pk17r/Ultimate_Tester/ComponentTester-1.54m/Arduino Mega Pinout.png

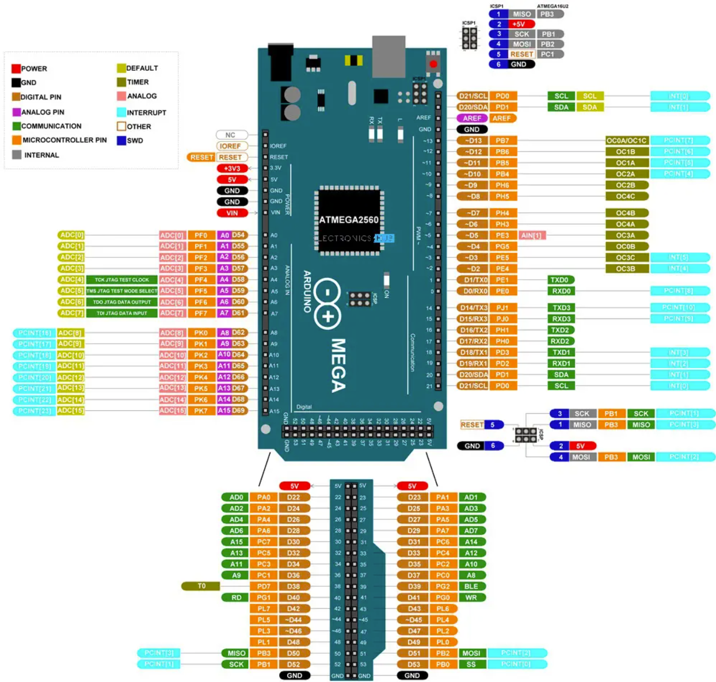
ComponentTester-1.54m/Arduino Mega Pinout.png
