pk17r/Ultimate_Tester/ComponentTester-1.54m/atmega1284p_pinout.png

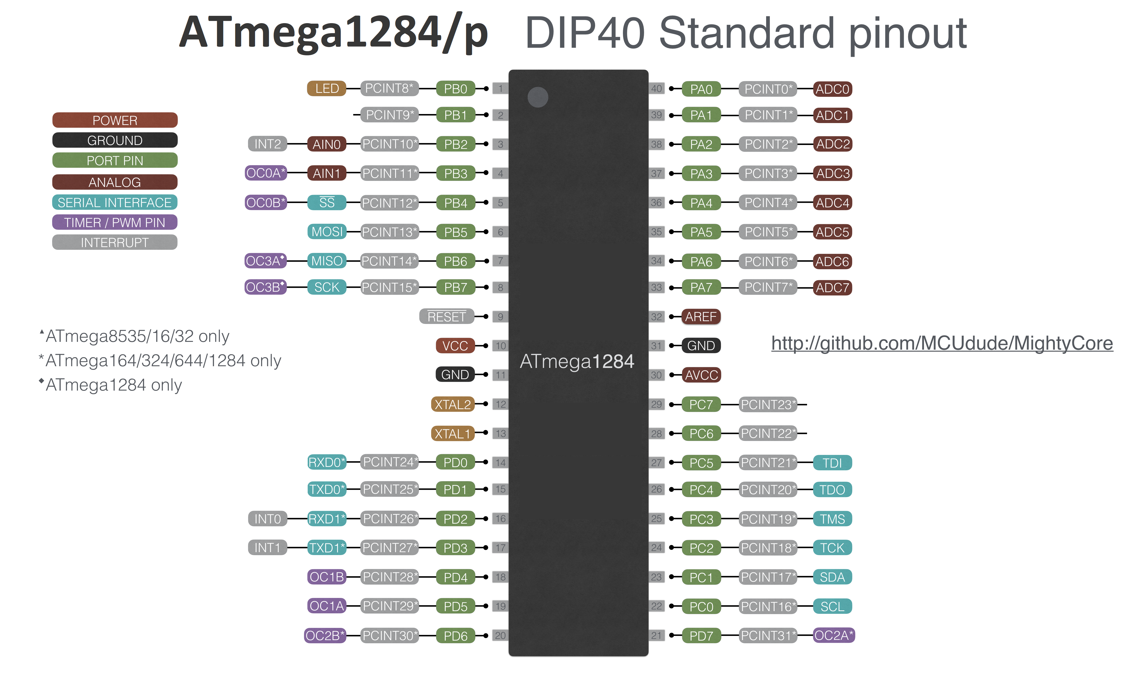
ComponentTester-1.54m/atmega1284p_pinout.png
