pk17r/Ultimate_Tester/Ultimate_Tester_PCBs/UltimateTester_v1_with_mods/Schematics.png

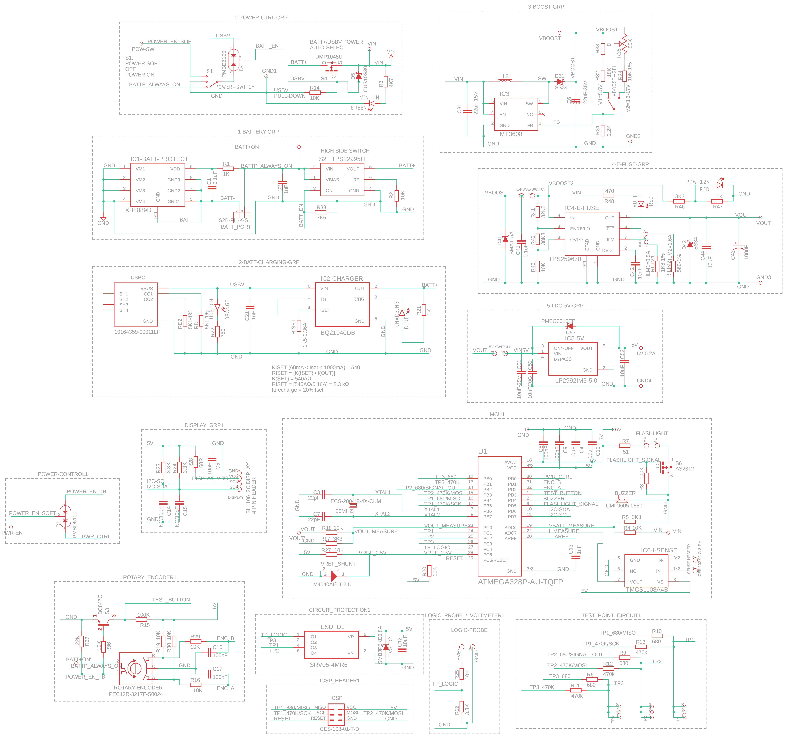
Ultimate_Tester_PCBs/UltimateTester_v1_with_mods/Schematics.png
