pk17r/Ultimate_Tester/ComponentTester-1.54m/AVR_Dudess_Settings.jpg

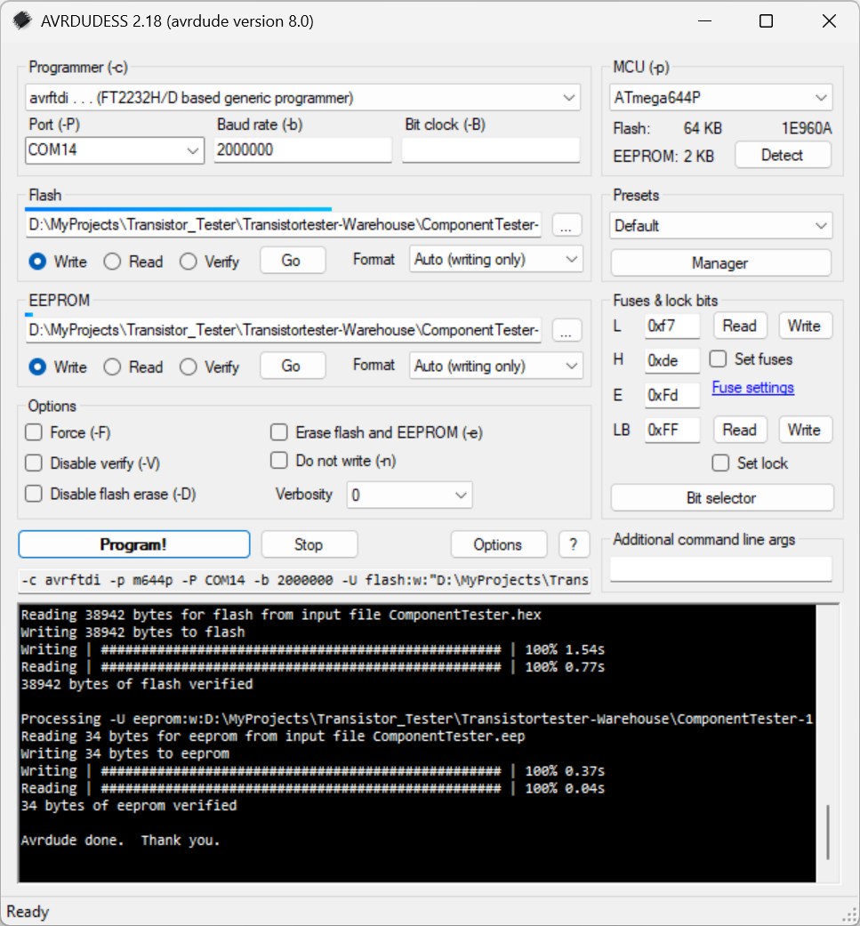
ComponentTester-1.54m/AVR_Dudess_Settings.jpg
