pk17r/Ultimate_Tester/Ultimate_Tester_PCBs/UltimateTester_v1_Pics/20250103_011226.jpg

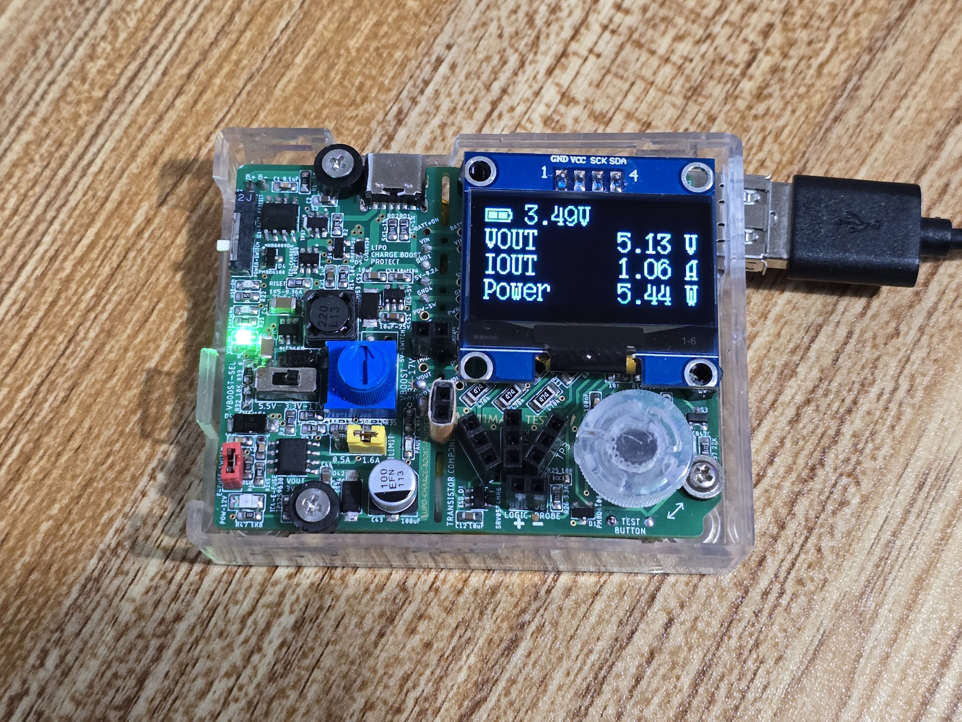
Ultimate_Tester_PCBs/UltimateTester_v1_Pics/20250103_011226.jpg
