pk17r/Ultimate_Tester/Ultimate_Tester_PCBs/UltimateTester_v1_Pics/img_0640.png

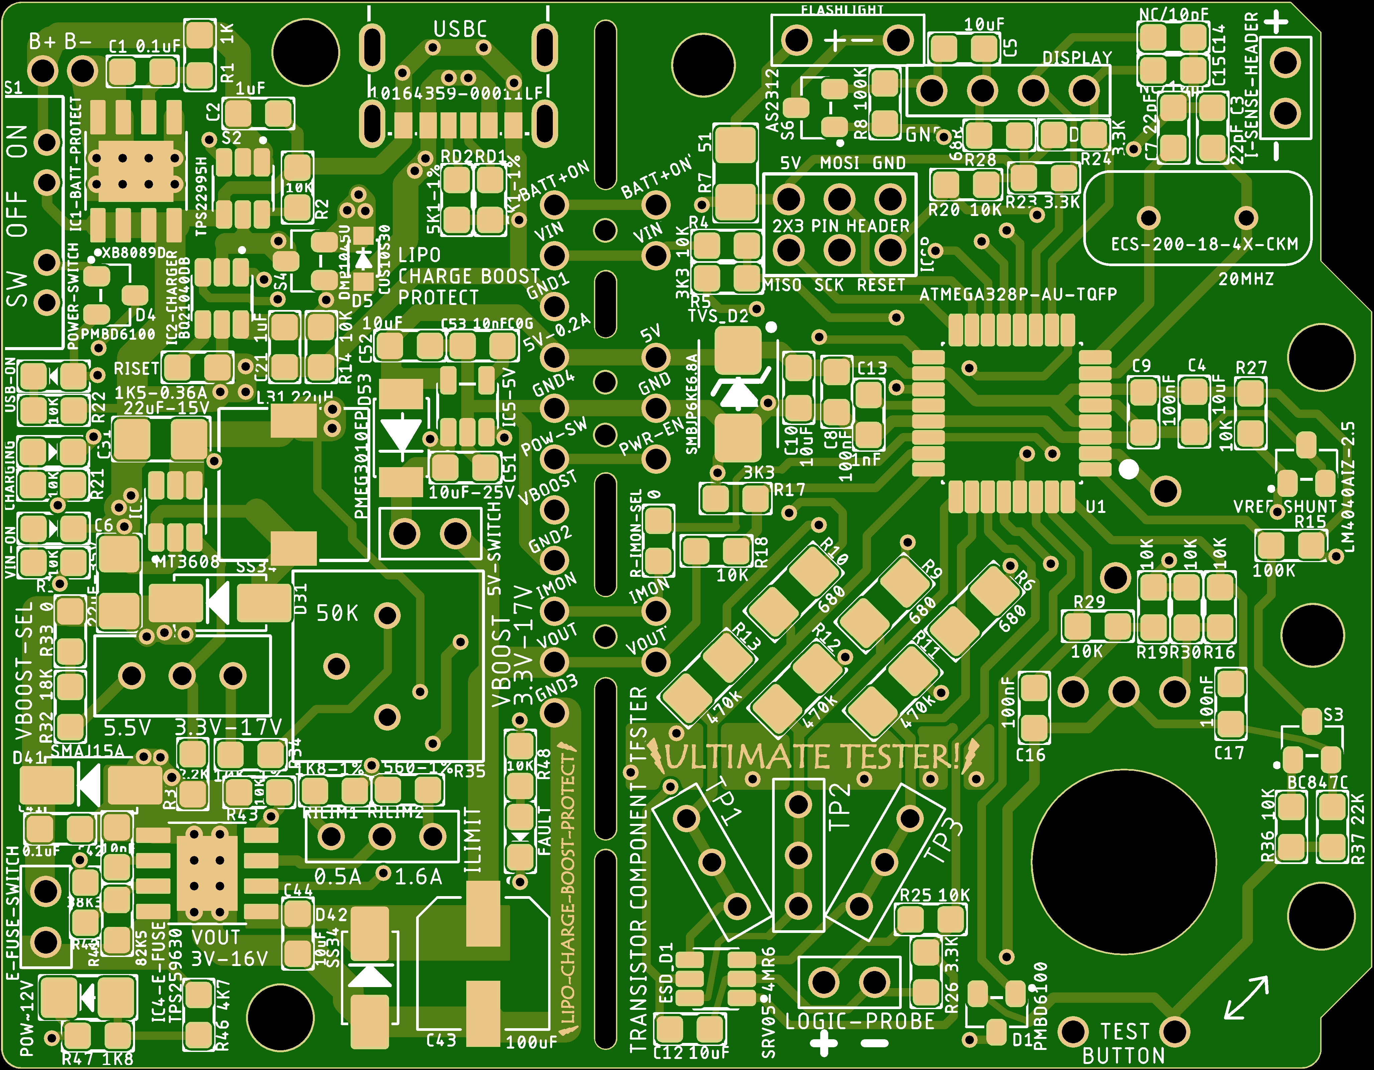
Ultimate_Tester_PCBs/UltimateTester_v1_Pics/img_0640.png
