pk17r/Ultimate_Tester/Ultimate_Tester_PCBs/UltimateTester_v1_Pics/img_0926.jpg

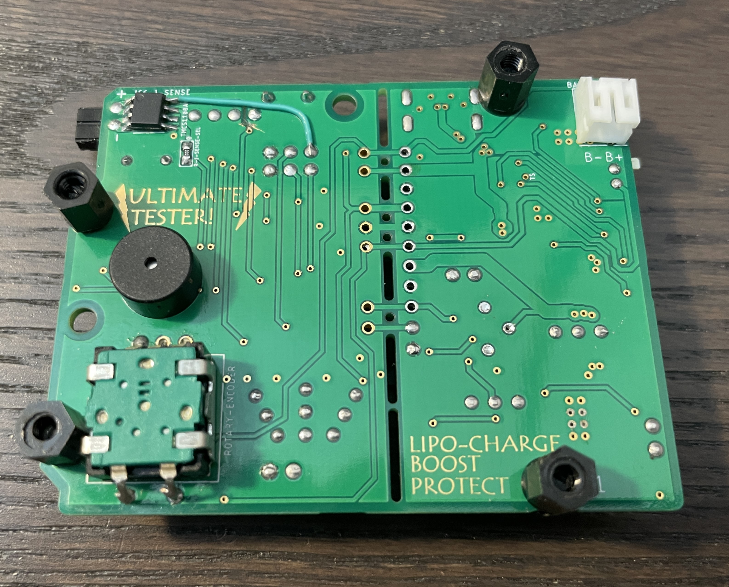
Ultimate_Tester_PCBs/UltimateTester_v1_Pics/img_0926.jpg
