pk17r/Ultimate_Tester/Ultimate_Tester_PCBs/UltimateTester_v1_Pics/main_image.jpg

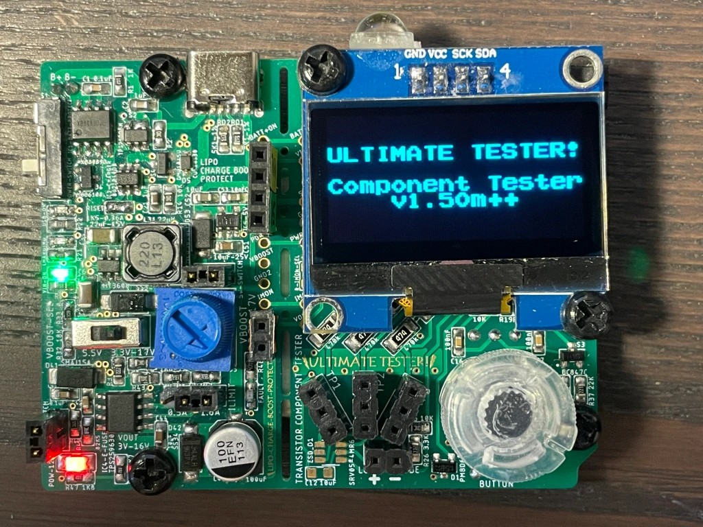
Ultimate_Tester_PCBs/UltimateTester_v1_Pics/main_image.jpg
