pk17r/Ultimate_Tester/Ultimate_Tester_PCBs/UltimateTester_v2.1/3D_UltimateTester_v2.1_2025-12-15_Btm.png

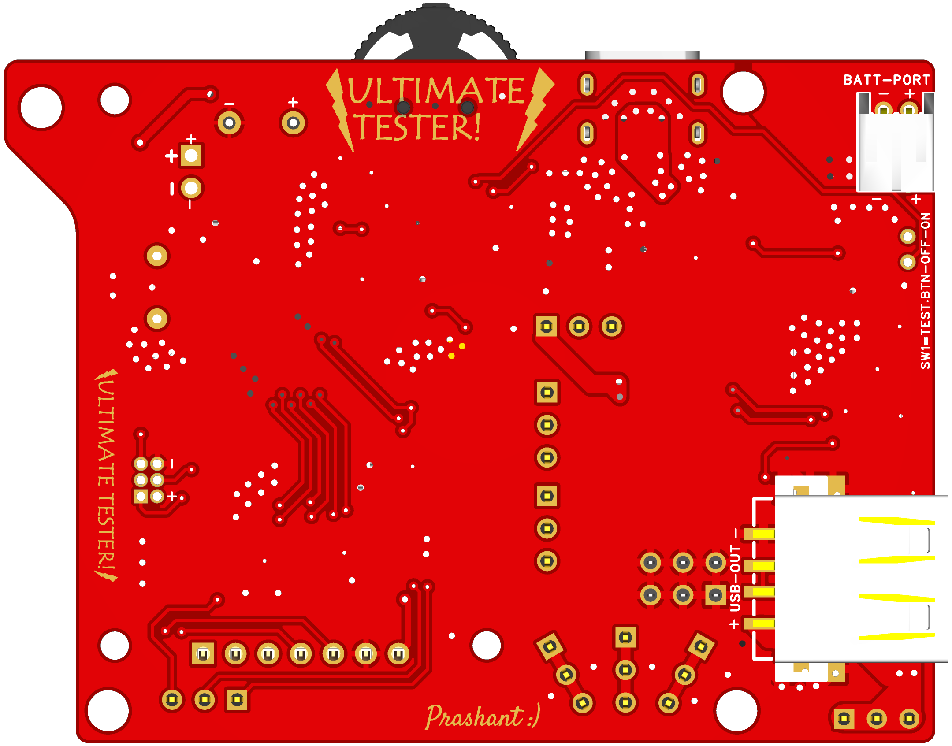
Ultimate_Tester_PCBs/UltimateTester_v2.1/3D_UltimateTester_v2.1_2025-12-15_Btm.png
