pk17r/Ultimate_Tester/Firmware/k-firmware/trunk/ReadInductance.c

// new code by K.-H. Kübbeler
// The 680 Ohm resistor (R_L_VAL) at the Lowpin will be used as current sensor
// The current with a coil will with (1 - e**(-t*R/L)), where R is
// the sum of Pin_RM , R_L_VAL , Resistance of coil and Pin_RP.
// L in the inductance of the coil.
#include <avr/io.h>
#include <stdlib.h>
#include "Transistortester.h"


//=================================================================
void ReadInductance(void) {
#if FLASHEND > 0x1fff
  // check if inductor and measure the inductance value
  unsigned int tmpint;
  unsigned int umax;
  unsigned int total_r;		// total resistance of current loop
  unsigned int mess_r;		// value of resistor used for current measurement
  unsigned long inductance[4];	// four inductance values for different measurements
  union t_combi{
  unsigned long dw;     // time_constant
  uint16_t w[2];
  } timeconstant;
  unsigned int resistor;
  uint8_t res_num;
  uint16_t per_ref1,per_ref2;	// percentage
  uint8_t LoPinR_L;	// Mask for switching R_L resistor of low pin
  uint8_t HiADC;	// Mask for switching the high pin direct to VCC
  uint8_t ii;
  uint8_t count;	// counter for the different measurements
  uint8_t cnt_diff;     // resistance dependent offset
  int8_t ukorr;		// correction of comparator voltage
  uint8_t nr_pol1;	// number of successfull inductance measurement with polarity 1
  uint8_t nr_pol2;	// number of successfull inductance measurement with polarity 2
  union {
  uint16_t pw;		// return value from Rnum2pins()
  uint8_t pb[2];	// the pin numbers LowPin and HighPin
  } rpins;	// resistor pin structure to prevent two return parameters


  inductor_lpre = 2;	// H units, mark inductor as 1, if resistor is too big
  if(PartFound != PART_RESISTOR) {
     return;	//We have found no resistor  
  }
  if (ResistorsFound != 1) {
     return;	// do not search for inductance, more than 1 resistor
  }
     res_num = ResistorList[0];
     if (ResistorVal[res_num] > 21000) return;
     resistor = ResistorVal[res_num];

     // we can check for Inductance, if resistance is below 2100 Ohm
     for (count=0;count<4;count++) {
        // Try four times (different direction and with delayed counter start)
        if (count < 2) {
           // first and second pass, direction 1
           rpins.pw = Rnum2pins(res_num);	// compute the two pinnumbers for resistor res_num
        } else {
           // third and fourth pass, direction 2
           rpins.pw = Rnum2pins(res_num);	// compute the two pinnumbers for resistor res_num
           ii = rpins.pb[0];
           rpins.pb[0] = rpins.pb[1];		// swap the pins LowPin and HighPin
           rpins.pb[1] = ii;
        }
#if (((PIN_RL1 + 1) != PIN_RH1) || ((PIN_RL2 + 1) != PIN_RH2) || ((PIN_RL3 + 1) != PIN_RH3))
        HiADC = pgm_read_byte((&PinRLRHADCtab[6])+rpins.pb[1]-TP1);	// Table of ADC Pins including | TXD_VAL
#else
        HiADC = pgm_read_byte((&PinRLRHADCtab[3])+rpins.pb[1]-TP1);	// Table of ADC Pins including | TXD_VAL
#endif
        LoPinR_L = pgm_read_byte(&PinRLRHADCtab[rpins.pb[0]]-TP1);	//R_L mask for HighPin R_L load
        //==================================================================================
        // Measurement of Inductance values
        R_PORT = 0;		// switch R port to GND
        ADC_PORT =   TXD_VAL;		// switch ADC-Port to GND
        if ((resistor < 240) && ((count & 0x01) == 0)) {
           // we can use PinR_L for measurement
           mess_r = RR680MI - R_L_VAL;			// use only pin output resistance
           ADC_DDR = HiADC | (1<<rpins.pb[0]) | TXD_MSK;	// switch HiADC and Low Pin to GND, 
        } else {
           R_DDR = LoPinR_L;   		// switch R_L resistor port for LowPin to output (GND)
           ADC_DDR = HiADC | TXD_MSK;	// switch HiADC Pin to GND 
           mess_r = RR680MI;			// use 680 Ohm and PinR_L for current measurement
        }
        // Look, if we can detect any current
        for (ii=0;ii<20;ii++) {
            // wait for current is near zero
            umax = W10msReadADC(rpins.pb[0]);
            total_r =  ReadADC(rpins.pb[1]);
            if ((umax < CAP_EMPTY_LEVEL) && (total_r < CAP_EMPTY_LEVEL)) break;	// low current detected
        }
        // setup Analog Comparator
        ADC_COMP_CONTROL = (1<<ACME);			//enable Analog Comparator Multiplexer
        ACSR =  (1<<ACBG) | (1<<ACI)  | (1<<ACIC);	// enable, 1.3V, no Interrupt, Connect to Timer1 
        ADMUX = (1<<REFS0) | rpins.pb[0];			// switch Mux to Low-Pin
        ADCSRA = (1<<ADIF) | AUTO_CLOCK_DIV; //disable ADC
   
      // setup Counter1
        timeconstant.w[1] = 0;		// set ov counter to 0
        TCCR1A = 0;			// set Counter1 to normal Mode
        TCNT1 = 0;			//set Counter to 0
        TI1_INT_FLAGS = (1<<ICF1) | (1<<OCF1B) | (1<<OCF1A) | (1<<TOV1);	// reset TIFR or TIFR1
//        HiADC |= TXD_VAL;
        wait200us();			// wait for bandgap to start up
        if ((count & 0x01) == 0 ) {
           //first start counter, then start current
           TCCR1B =  (1<<ICNC1) | (0<<ICES1) | (1<<CS10);	//start counter 1MHz or 8MHz
           ADC_PORT = HiADC;		// switch ADC-Port to VCC
        } else {
           //first start current, then start counter with delay
           //parasitic capacity of coil can cause high current at the beginning
           ADC_PORT = HiADC;		// switch ADC-Port to VCC
      #if F_CPU >= 8000000UL
           wait3us();		// ignore current peak from capacity
      #else
           wdt_reset();			// delay
           wdt_reset();			// delay
      #endif
           TI1_INT_FLAGS = (1<<ICF1);	// Reset Input Capture
           TCCR1B =  (1<<ICNC1) | (0<<ICES1) | (1<<CS10);	//start counter 1MHz or 8MHz
        }
      
      //******************************
        while(1) {
           // Wait, until  Input Capture is set
           ii = TI1_INT_FLAGS;		//read Timer flags
           if (ii & (1<<ICF1))  {
              break;
           }
           if((ii & (1<<TOV1))) {		// counter overflow, 65.536 ms @ 1MHz, 8.192ms @ 8MHz
              TI1_INT_FLAGS = (1<<TOV1);	// Reset OV Flag
              wdt_reset();
              timeconstant.w[1]++;		// count one OV
              if(timeconstant.w[1] == (F_CPU/100000UL)) {
                 break; 	//Timeout for Charging, above 0.65 s
              }
           }
        }
        ADC_PORT = TXD_VAL;		// switch ADC-Port to GND
        TCCR1B = (0<<ICNC1) | (0<<ICES1) | (0<<CS10);  // stop counter
        TI1_INT_FLAGS = (1<<ICF1);			// Reset Input Capture
        timeconstant.w[0] = ICR1;		// get previous Input Capture Counter flag
      // check actual counter, if an additional overflow must be added
        if((TCNT1 > timeconstant.w[0]) && (ii & (1<<TOV1))) {
           // this OV was not counted, but was before the Input Capture
           TI1_INT_FLAGS = (1<<TOV1);		// Reset OV Flag
           timeconstant.w[1]++;			// count one additional OV
        }

//        ADC_PORT = TXD_VAL;		// switch ADC-Port to GND
        ADCSRA = (1<<ADEN) | (1<<ADIF) | AUTO_CLOCK_DIV; //enable ADC
        for (ii=0;ii<20;ii++) {
            // wait for current is near zero
            umax = W10msReadADC(rpins.pb[0]);
            total_r =  ReadADC(rpins.pb[1]);
            if ((umax < CAP_EMPTY_LEVEL) && (total_r < CAP_EMPTY_LEVEL)) break;	// low current detected
        }  /* end for ii */
  #define CNT_ZERO_42 6
  #define CNT_ZERO_720 7
//#if F_CPU == 16000000UL
//  #undef CNT_ZERO_42
//  #undef CNT_ZERO_720
//  #define CNT_ZERO_42 7
//  #define CNT_ZERO_720 10
//#endif
        total_r = (mess_r + resistor + RRpinMI);
//        cnt_diff = 0;
//        if (total_r > 7000) cnt_diff = 1;
//        if (total_r > 14000) cnt_diff = 2;
        cnt_diff = total_r / ((14000UL * 8) / (F_CPU/1000000UL));
        tmpint = ref_mv_offs;		// corrected reference voltage (for C)
        if (mess_r < R_L_VAL) {
           // measurement without 680 Ohm
           cnt_diff = CNT_ZERO_42;
           if (timeconstant.dw < 225) {
              ukorr = (timeconstant.w[0] / 5) - 20;
           } else {
              ukorr = 25;
           }
           tmpint -= (((REF_L_KORR * 10) / 10) + ukorr);
        } else {
           // measurement with 680 Ohm resistor
           // if 680 Ohm resistor is used, use REF_L_KORR for correction
           cnt_diff += CNT_ZERO_720;
           tmpint += REF_L_KORR;
        }
        if (timeconstant.dw > cnt_diff) timeconstant.dw -= cnt_diff;
        else          timeconstant.dw = 0;
       
        if ((count&0x01) == 1) {
           // second pass with delayed counter start
           timeconstant.dw += (3 * (F_CPU/1000000UL))+10;
        }
        if (timeconstant.w[1] >= (F_CPU/100000UL)) timeconstant.dw = 0; // no transition found
        if (timeconstant.dw > 10) {
           timeconstant.dw -= 1;
        }
        // compute the maximum Voltage umax with the Resistor of the coil
        umax = ((unsigned long)mess_r * (unsigned long)ADCconfig.U_AVCC) / total_r;
        per_ref1 = ((unsigned long)tmpint * 1000) / umax;
//        per_ref2 = (uint8_t)MEM2_read_byte(&LogTab[per_ref1]);	// -log(1 - per_ref1/100)
        per_ref2 = get_log(per_ref1);		// -1000*log(1 - per_ref1/1000)
/* ********************************************************* */
#if 0
          if (count == 0) {
             lcd_line3();
             DisplayValue(count,0,' ',4);
             DisplayValue(timeconstant.dw,0,'+',4);
             DisplayValue(cnt_diff,0,' ',4);
             DisplayValue(total_r,-1,'r',4);
             lcd_space();
             DisplayValue(per_ref1,-1,'%',4);
             lcd_line4();
             Display_mV(tmpint,4);
             lcd_space();
             Display_mV(umax,4);
             lcd_space();
             DisplayValue(per_ref2,-1,'%',4);
             wait_about4s();	// debug delay
             wait_about2s();	// debug delay
          }
#endif
/* ********************************************************* */
        // inductor_lx in 0.01mH units,  L = Tau * R
        per_ref1 = ((per_ref2 * (F_CPU/1000000UL)) + 5) / 10;
        inductance[count] = (timeconstant.dw * total_r ) / per_ref1;
        if (((count&0x01) == 0) && (timeconstant.dw > ((F_CPU/1000000UL)+3))) {
           // transition is found, measurement with delayed counter start is not necessary
           inductance[count+1] = inductance[count];	// set delayed measurement to same value
           count++;		// skip the delayed measurement
        }
        wdt_reset();
     }  //end for count
     ADC_PORT = TXD_VAL;		// switch ADC Port to GND
     wait_about20ms();
     nr_pol1 = 0;
     if (inductance[1] > inductance[0]) { nr_pol1 = 1; } 
     nr_pol2 = 2;
     if (inductance[3] > inductance[2]) { nr_pol2 = 3; } 
     if (inductance[nr_pol2] < inductance[nr_pol1]) nr_pol1 = nr_pol2;
     inductor_lx = inductance[nr_pol1];
     inductor_lpre = -5;	// 10 uH units
     if (((nr_pol1 & 1) == 1) || (resistor >= 240)) {
        // with 680 Ohm resistor total_r is more than 7460
        inductor_lpre = -4;	// 100 uH units
        inductor_lx = (inductor_lx + 5) / 10;
     } 
     if (inductor_lx == 0) inductor_lpre = 0;	//mark as zero

  // switch all ports to input
  ADC_DDR =  TXD_MSK;		// switch all ADC ports to input
  R_DDR = 0;			// switch all resistor ports to input
#endif
  return;
 } // end ReadInductance()
