pk17r/Ultimate_Tester/TT+ADS1115/ads1115.c

#include <util/delay.h>
#include "ads1115.h"

//*************************************************************************
//  write register of ADC
uint8_t ads1115_write_register(uint8_t addr, uint8_t reg, uint16_t data){	
	i2c_start_wait((addr << 1) + I2C_WRITE);
	i2c_write((uint8_t)reg);
	i2c_write((uint8_t)(data >> 8));
	i2c_write((uint8_t)(data & 0xFF));
	i2c_stop();
	return 0;
}

//*************************************************************************
// read register from ADC
uint16_t ads1115_read_register(uint8_t addr, uint8_t reg){
	i2c_start_wait((addr << 1) + I2C_WRITE);
	i2c_write(reg);
	i2c_stop();
	
	i2c_rep_start((addr << 1) + I2C_READ);
	uint8_t msb = i2c_readAck();
	uint8_t lsb = i2c_readNak();
	i2c_stop();
	
	uint16_t data = (msb << 8 | lsb);
	return data;
}

//*************************************************************************
// read raw data from one channel of ADC
uint16_t ads1115_readADC_SingleEnded(uint8_t addr, uint8_t channel, ads1115_datarate dr, ads1115_fsr_gain gain){
	// Check channel number
	if(channel > 3) return 0;
	
	uint16_t adc_config = ADS1115_COMP_QUE_DIS	|
				 ADS1115_COMP_LAT_NonLatching |
				 ADS1115_COMP_POL_3_ACTIVELOW |	
				 ADS1115_COMP_MODE_TRADITIONAL | 
				 dr |
				 ADS1115_MODE_SINGLE | 
				 gain;
	
	if(channel == 0)	adc_config |= ADS1115_MUX_AIN0_GND;
	else if(channel == 1)	adc_config |= ADS1115_MUX_AIN1_GND;
	else if(channel == 2)	adc_config |= ADS1115_MUX_AIN2_GND;
	else if(channel == 3)	adc_config |= ADS1115_MUX_AIN3_GND;
	
	adc_config |= ADS1115_OS_SINGLE;	
	
	ads1115_write_register(addr, ADS1115_REG_CONFIG, adc_config);
	_delay_ms(8);
		
	return ads1115_read_register(addr, ADS1115_REG_CONVERSION) >> 0;
}
