pk17r/Ultimate_Tester/Firmware/k-firmware/trunk/langSPANISH.h

#if defined(LANG_SPANISH)
   const unsigned char TestRunning[] MEM_TEXT = "Testeando...";	
   const unsigned char BatWeak[] MEM_TEXT = "Poca bateria"; 	
   const unsigned char BatEmpty[] MEM_TEXT = "Sin bateria"; 	
   const unsigned char TestFailed2[] MEM_TEXT = "Pieza "; 	
   const unsigned char Bauteil[] MEM_TEXT = "mal..."; 		
//   const unsigned char Diode[] MEM_TEXT = "Diodo: ";
   const unsigned char Triac[] MEM_TEXT = "Triac";
   const unsigned char Thyristor[] MEM_TEXT = "Tiristor";
   const unsigned char Unknown[] MEM_TEXT = "No se ?"; 	
   const unsigned char TestFailed1[] MEM_TEXT = "Componente mal"; 
   const unsigned char OrBroken[] MEM_TEXT = " o roto "; 
   const unsigned char TestTimedOut[] MEM_TEXT = "Tiempo agotado!";
   #define Cathode_char 'K'
 #ifdef WITH_SELFTEST
   const unsigned char SELFTEST[] MEM_TEXT = "Calibracion...";
   const unsigned char RELPROBE[] MEM_TEXT = "Aislar Puntas!";
   const unsigned char ATE[] MEM_TEXT = "Fin de Cal.";
 #endif
 #ifdef WITH_MENU
   const unsigned char SELECTION_str[] MEM2_TEXT = "Seleccion:";
   const unsigned char TESTER_str[] MEM2_TEXT = "Transistor";
   const unsigned char FREQ_str[] MEM2_TEXT = "Frequencia";
   const unsigned char VOLTAGE_str[] MEM2_TEXT = "Voltage";
   const unsigned char SHOW_str[] MEM2_TEXT = "mostrar datos";	
   const unsigned char OFF_str[] MEM2_TEXT = "desconectar";
   const unsigned char F_GEN_str[] MEM2_TEXT = "F-Generador";
  #ifdef PWM_SERVO
   const unsigned char PWM_10bit_str[] MEM2_TEXT = "Servo PWM";
  #else
   const unsigned char PWM_10bit_str[] MEM2_TEXT = "10-bit PWM";
  #endif
  #ifdef WITH_ROTARY_CHECK
   const unsigned char RotaryEncoder_str[] MEM2_TEXT = "encoder rotativo";
  #endif
   const unsigned char SetCapCorr_str[] MEM2_TEXT = {'C','(',LCD_CHAR_U,'F',')','-','C','o','r','r','e','c','c','i','o','n',0};
   const unsigned char TURN_str[] MEM2_TEXT = "rotar!";
   const unsigned char FULLCHECK_str[] MEM2_TEXT = "Calibracion...";
   const unsigned char SHORT_PROBES_str[] MEM2_TEXT = "Cortocircuite las puntas!";
  #if PROCESSOR_TYP == 644
   const unsigned char HFREQ_str[] MEM2_TEXT = "Frequencia > 2MHz";
   const unsigned char H_CRYSTAL_str[] MEM2_TEXT = "HF cristal";
   const unsigned char L_CRYSTAL_str[] MEM2_TEXT = "LF cristal";
  #endif
  #if ((LCD_ST_TYPE == 7565) || (LCD_ST_TYPE == 1306) || (LCD_ST_TYPE == 8812) || (LCD_ST_TYPE == 8814) || (LCD_ST_TYPE == 8814) || defined(LCD_DOGM))
   const unsigned char CONTRAST_str[] MEM2_TEXT = "Contraste";
  #endif
 #endif  /* WITH_MENU */
 #ifdef WITH_XTAL
   const unsigned char cerres_str[] MEM_TEXT = "Cer.resonator  ";
   const unsigned char xtal_str[] MEM_TEXT = "Cristal  ";
 #endif
 #define LANG_SELECTED
#endif  /* LANG SPANISH */
