pk17r/Ultimate_Tester/ComponentTester-1.54m/Files/main.c

/* ************************************************************************
 *
 *   main part
 *
 *   (c) 2012-2024 by Markus Reschke
 *   based on code from Markus Frejek and Karl-Heinz Kübbeler
 *
 * ************************************************************************ */


/*
 *  local constants
 */

/* source management */
#define MAIN_C


/*
 *  include header files
 */

/* local includes */
#include "config.h"           /* global configuration */
#include "common.h"           /* common header file */
#include "variables.h"        /* global variables */
#include "functions.h"        /* external functions */
#include "colors.h"           /* color definitions */


/*
 *  local variables
 */

/* program control */
#if CYCLE_MAX < 255
uint8_t        MissedParts;          /* counter for failed/missed components */
#endif


/* ************************************************************************
 *   output components and errors
 * ************************************************************************ */


/*
 *  get pin designator for specific probe ID
 *
 *  requires:
 *  - probe ID [0-2]
 *
 *  returns:
 *  - pin designator
 */

uint8_t Get_SemiPinDesignator(uint8_t Probe)
{
  uint8_t           Char;          /* designator / return value */

  /* looking for matching probe ID */
  if (Probe == Semi.A)             /* matches pin A */
  {
    Char = Semi.DesA;              /* designator for pin A */
  }
  else if (Probe == Semi.B)        /* matches pin B */
  {
    Char = Semi.DesB;              /* designator for pin B */
  }
  else                             /* matches pin C */
  {
    Char = Semi.DesC;              /* designator for pin C */
  }

  return Char;
}



#if ! defined (UI_NO_TEXTPINOUT) || defined (SW_ENCODER)

/*
 *  show pinout for semiconductors
 *  - displays: 123=abc
 */

void Show_SemiPinout(void)
{
  uint8_t           n;             /* counter */

  /* display: 123 */
  for (n = 0; n <= 2; n++)         /* loop through probe pins */
  {
    Display_ProbeNumber(n);        /* display probe ID */
  }

  /* display: = */
  Display_Char('=');

  /* display pin designators */
  for (n = 0; n <= 2; n++)         /* loop through probe pins */
  {
    Display_SemiPinDesignator(n);  /* display pin designator */
  }
}

#endif



/*
 *  show simple pinout
 *  - displays: 1:a 2:b 3:c 
 *
 *  required:
 *  - DesX: designators for probes #1, #2 and #3
 *    0 -> not displayed
 */

void Show_SimplePinout(uint8_t Des1, uint8_t Des2, uint8_t Des3)
{
  uint8_t           n;        /* counter */
  unsigned char     Des[3];   /* component pin designators */
  #ifdef UI_PROBE_COLORS
  uint16_t          Color;    /* color value */

  Color = UI.PenColor;             /* save current color */
  #endif

  /* copy probe pin designators */
  Des[0] = Des1;
  Des[1] = Des2;
  Des[2] = Des3;

  for (n = 0; n <= 2; n++)         /* loop through probe pins */
  {
    if (Des[n] != 0)               /* display this one */
    {
      Display_ProbeNumber(n);
      Display_Colon();

      #ifdef UI_PROBE_COLORS
      UI.PenColor = ProbeColors[n];     /* set probe color */
      #endif

      Display_Char(Des[n]);

      #ifdef UI_PROBE_COLORS
      UI.PenColor = Color;              /* restore old color */
      #endif

      Display_Space();
    }
  }
}



#ifdef FUNC_EVALUE

/*
 *  show E series norm values
 *
 *  requires:
 *  - Value: unsigned value
 *  - Scale: exponent/multiplier (* 10^n)
 *  - ESeries: E6-192
 *  - Tolerance: in 0.1%
 *  - Unit: unit character
 */

void Show_ENormValues(uint32_t Value, int8_t Scale, uint8_t ESeries, uint8_t Tolerance, unsigned char Unit)
{
  uint8_t           n;             /* number of norm values (1 or 2) */
  uint8_t           Pos;           /* char x position */
  uint8_t           Temp;          /* temporary value */


  /*
   *  get E series norm values
   *  - 1st: Semi.I_value, Semi.I_scale
   *  - 2nd: Semi.C_value, Semi.C_scale
   */

  n = GetENormValue(Value, Scale, ESeries, Tolerance);


  /*
   *  show E series and tolerance
   */

  Display_NextLine();                   /* move to next line */

  /* display E series */
  Display_Char('E');                    /* display: E */
  Display_FullValue(ESeries, 0 , 0);    /* display E series */

  Display_Space();                      /* display: " " */

  /* display tolerance */
  Temp = Tolerance;                     /* copy tolerance */
  Pos = 0;                              /* reset decimal places */

  if (Temp < 10)                        /* < 1% */
  {
    Pos = 1;                            /* one decimal place */
  }
  Temp /= 10;                           /* scale to 1 */

  Display_FullValue(Temp, Pos, '%');    /* display tolerance */

  Display_Space();                      /* display: " " */


  /*
   *  show norm values
   */

  if (n)                      /* got norm value(s) */
  {
    Pos = UI.CharPos_X;       /* get current char position */

    /* display first norm value */
    Display_EValue(Semi.I_value, Semi.I_scale, Unit);

    if (n == 2)               /* got two norm values */
    {
      /* move to next line at same position (after E series) */
      Display_NextLine();
      LCD_CharPos(Pos, UI.CharPos_Y);

      /* display second norm value */
      Display_EValue(Semi.C_value, Semi.C_scale, Unit);
    }
  }
  else                        /* no norm value */
  {
    Display_Minus();          /* display: - */
  }
}

#endif



#ifdef FUNC_COLORCODE

/*
 *  show E series norm values as color-code
 *
 *  requires:
 *  - Value: unsigned value
 *  - Scale: exponent/multiplier (* 10^n)
 *  - ESeries: E6-192
 *  - Tolerance: in 0.1%
 *  - TolBand: color of tolerance band
 */

void Show_ENormCodes(uint32_t Value, int8_t Scale, uint8_t ESeries, uint8_t Tolerance, uint16_t TolBand)
{
  uint8_t           n;             /* number of norm values (1 or 2) */
  uint8_t           Pos;           /* char x position */

  /*
   *  tolerance band
   *  - resistor
   *    20%  10%    5%   2%  1%    0.5%  0.25% 0.1%   0.05%
   *    none silver gold red brown green blue  violet grey
   *  - inductor
   *    20%   10%    5%   4%     3%     2%  1%    0.5%  0.25% 0.1%   0.05%
   *    black silver gold yellow orange red brown green blue  violet grey
   *  - caps: many different schemas
   *
   *  multiplier reference
   *  - R:   0 (10^0)   -> 1 Ohms
   *    C: -12 (10^-12) -> 1 pF
   *    L:  -6 (10^-6)  -> 1 µH
   *  - ref_scale as function argument?
   *    scale = scale - ref_scale
   */

  /*
   *  get E series norm values
   *  - 1st: Semi.I_value, Semi.I_scale
   *  - 2nd: Semi.C_value, Semi.C_scale
   */

  n = GetENormValue(Value, Scale, ESeries, Tolerance);


  /*
   *  show E series
   */

  Display_NextLine();                   /* move to next line */

  /* display E series */
  Display_Char('E');                    /* display: E */
  Display_FullValue(ESeries, 0 , 0);    /* display E series */

  Display_Space();                      /* display: " " */


  /*
   *  show color-codes of norm values
   */

  if (n)                      /* got norm value(s) */
  {
    Pos = UI.CharPos_X;       /* get current char position */

    /* display color-code of first norm value */
    Display_ColorCode(Semi.I_value, Semi.I_scale, TolBand);

    if (n == 2)               /* got two norm values */
    {
      /* move to next line at same position (after E series) */
      Display_NextLine();
      LCD_CharPos(Pos, UI.CharPos_Y);

      /* display color-code of second norm value */
      Display_ColorCode(Semi.C_value, Semi.C_scale, TolBand);
    }
  }
  else                        /* no norm value */
  {
    Display_Minus();          /* display: - */
  }

  #if 0
  /*
   *  color testing
   */

  uint16_t Color;

  Display_NextLine();

  /* first 5 colors plus gold */
  n = 0;
  while (n < 5)
  {
    Color = DATA_read_word((uint16_t *)&ColorCode_table[n]);
    LCD_Band(Color, ALIGN_LEFT);
    n++;
  }
  LCD_Band(COLOR_CODE_GOLD, ALIGN_RIGHT);

  Display_NextLine();

  /* last 5 colors plus silver */
  while (n < 10)
  {
    Color = DATA_read_word((uint16_t *)&ColorCode_table[n]);
    LCD_Band(Color, ALIGN_LEFT);
    n++;
  }
  LCD_Band(COLOR_CODE_SILVER, ALIGN_RIGHT);

  TestKey(0, CURSOR_BLINK);
  #endif
}

#endif



#ifdef FUNC_EIA96

/*
 *  show E series norm values as EIA-96 code
 *  - implies E96 1%
 *
 *  requires:
 *  - Value: unsigned value
 *  - Scale: exponent/multiplier (* 10^n)
 */

void Show_ENormEIA96(uint32_t Value, int8_t Scale)
{
  uint8_t           n;             /* number of norm values (1 or 2) */

  /*
   *  get E series norm values
   *  - 1st: Semi.I_value, Semi.I_scale, Semi.A (index number)
   *  - 2nd: Semi.C_value, Semi.C_scale, Semi.B (index number)
   */

  n = GetENormValue(Value, Scale, E96, 10);

  /*
   *  show E series and tolerance
   */

  Display_NextLine();                   /* move to next line */

  /* display E series (E96) */
  Display_Char('E');                    /* display: E */
  Display_FullValue(96, 0, 0);          /* display E series */

  Display_Space();                      /* display: " " */

  /* display tolerance (1%) */
  Display_FullValue(1, 0, '%');         /* display tolerance */

  Display_Space();                      /* display: " " */


  /*
   *  show EIA-96 codes of norm values
   */

  if (n)                      /* got norm value(s) */
  {
    /* display EIA-96 code of first norm value */
    Display_EIA96(Semi.A, Semi.I_scale);

    if (n == 2)               /* got two norm values */
    {
      Display_Space();                  /* display: " " */

      /* display EIA-96 code of second norm value */
      Display_EIA96(Semi.B, Semi.C_scale);
    }
  }
  else                        /* no norm value */
  {
    Display_Minus();          /* display: - */
  }
}

#endif



/*
 *  show failed test
 *  - no component found
 */

void Show_Fail(void)
{
  /* display info */
  #ifdef UI_CENTER_ALIGN
    Display_CenterLine(2);                        /* center block: 2 lines */
    Display_EEString_Center(Failed1_str);         /* display: No component */
    Display_NL_EEString_Center(Failed2_str);      /* display: found! */
  #else
    Display_EEString(Failed1_str);      /* display: No component */
    Display_NL_EEString(Failed2_str);   /* display: found! */
  #endif

  #ifdef UI_QUESTION_MARK
  /* display question mark symbol */
  Check.Symbol = SYMBOL_QUESTIONMARK;   /* set symbol ID */
    #ifdef UI_CENTER_ALIGN
      Display_FancySemiPinout(1);       /* show symbol starting in line #1 */
    #else
      Display_FancySemiPinout(3);       /* show symbol starting in line #3 */
    #endif
  #endif

  #if CYCLE_MAX < 255
  MissedParts++;              /* increase counter */
  #endif
}



/*
 *  show error
 */

void Show_Error()
{
  if (Check.Type == TYPE_DISCHARGE)          /* discharge failed */
  {
    /* possibly a voltage source */
    Display_EEString(DischargeFailed_str);   /* display: Battery? */

    /* display probe number and remaining voltage */
    Display_NextLine();
    Display_ProbeNumber(Check.Probe);
    Display_Colon();
    Display_Space();
    Display_Value(Check.U, -3, 'V');
  }
  else if (Check.Type == TYPE_DETECTION)     /* detection error */
  {
    /* simply display: No component found! */
    Show_Fail();
  }
}



#ifdef UI_PROBE_COLORS

/*
 *  show single (first) resistor
 *
 *  requires:
 *  - Probe1: probe ID #1 [0-2]
 *  - Probe2: probe ID #2 [0-2]
 *  - Mode: 0 for probe ID
 *          >0 for pin designator
 */

void Show_SingleResistor(uint8_t Probe1, uint8_t Probe2, int8_t Mode)
{
  Resistor_Type     *Resistor;     /* pointer to resistor */

  Resistor = &Resistors[0];        /* pointer to first resistor */

  /*
   *  show pinout
   */

  if (Mode)
  {
    Display_SemiPinDesignator(Probe1);
  }
  else
  {
    Display_ProbeNumber(Probe1);
  }

  Display_EEString(Resistor_str);

  if (Mode)
  {
    Display_SemiPinDesignator(Probe2); 
  }
  else
  {
    Display_ProbeNumber(Probe2);
  }

  /* show resistance value */
  Display_Space();
  Display_Value(Resistor->Value, Resistor->Scale, LCD_CHAR_OMEGA);
}

#else

/*
 *  show single (first) resistor
 *
 *  requires:
 *  - ID1: pin ID #1 character
 *  - ID2: pin ID #2 character
 */

void Show_SingleResistor(uint8_t ID1, uint8_t ID2)
{
  Resistor_Type     *Resistor;     /* pointer to resistor */

  Resistor = &Resistors[0];        /* pointer to first resistor */

  /* show pinout */
  Display_Char(ID1);
  Display_EEString(Resistor_str);
  Display_Char(ID2); 

  /* show resistance value */
  Display_Space();
  Display_Value(Resistor->Value, Resistor->Scale, LCD_CHAR_OMEGA);
}

#endif



/*
 *  show resistor(s)
 */
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
